nansphilip/Splitergoll/Images/IMG_7818.webp

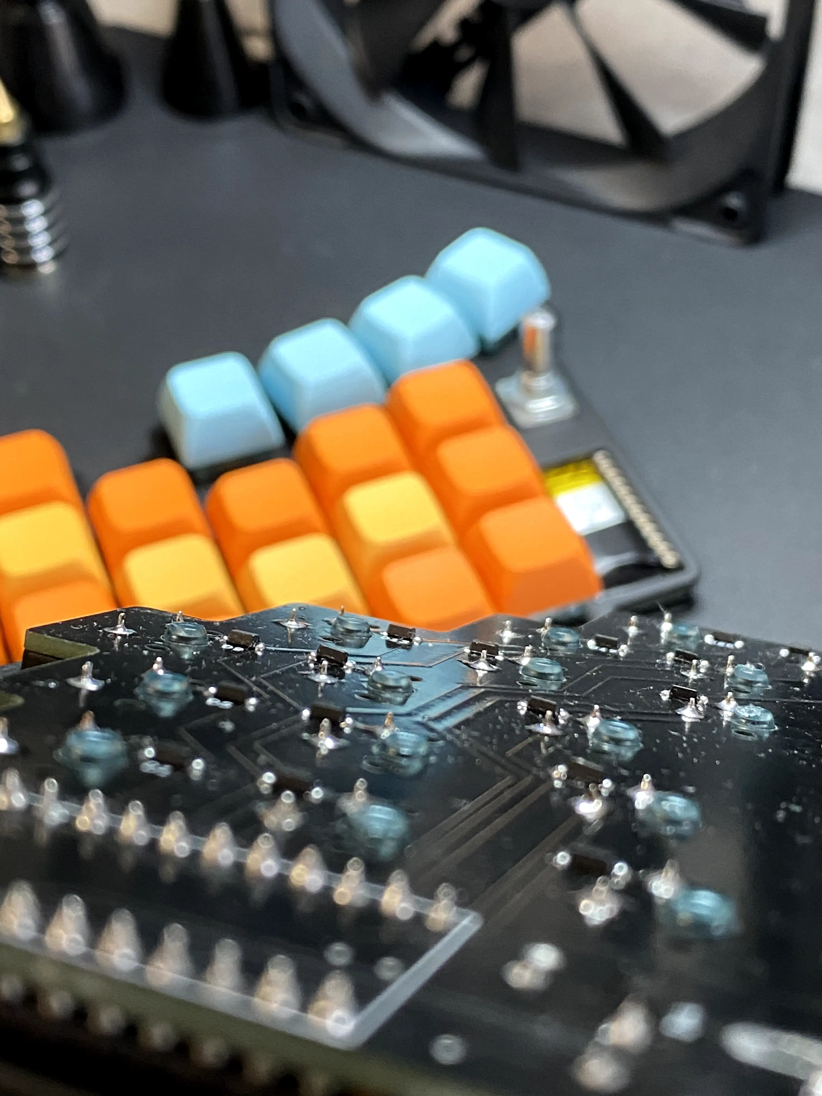
Images/IMG_7818.webp
