nansphilip/Splitergoll/Images/IMG_7819.webp

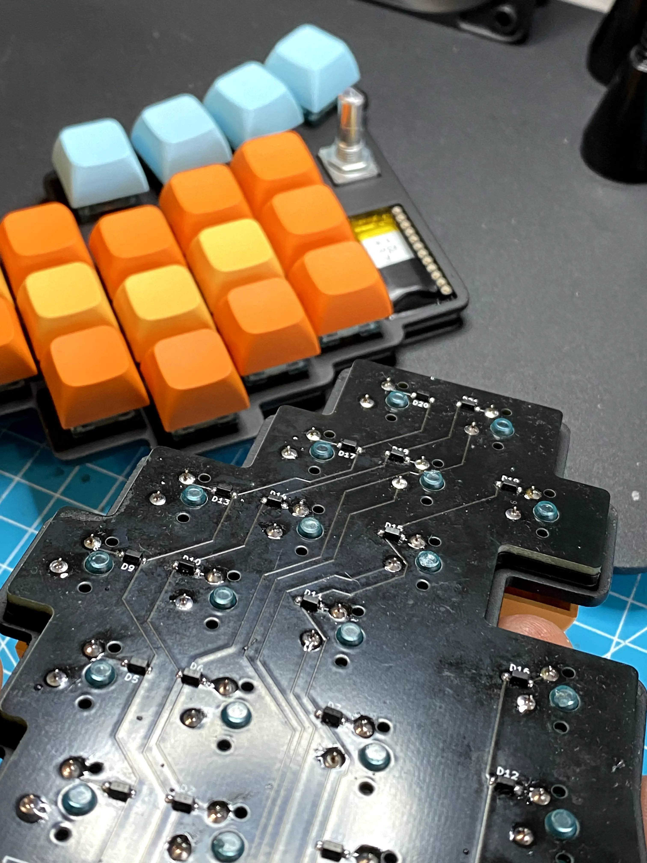
Images/IMG_7819.webp
